pylover/fridgecon/schematic/fridgecon/fridgecon.kicad_sch

## KiCad design schematic/fridgecon/fridgecon.kicad_sch (2025-06-11, an earlier design)

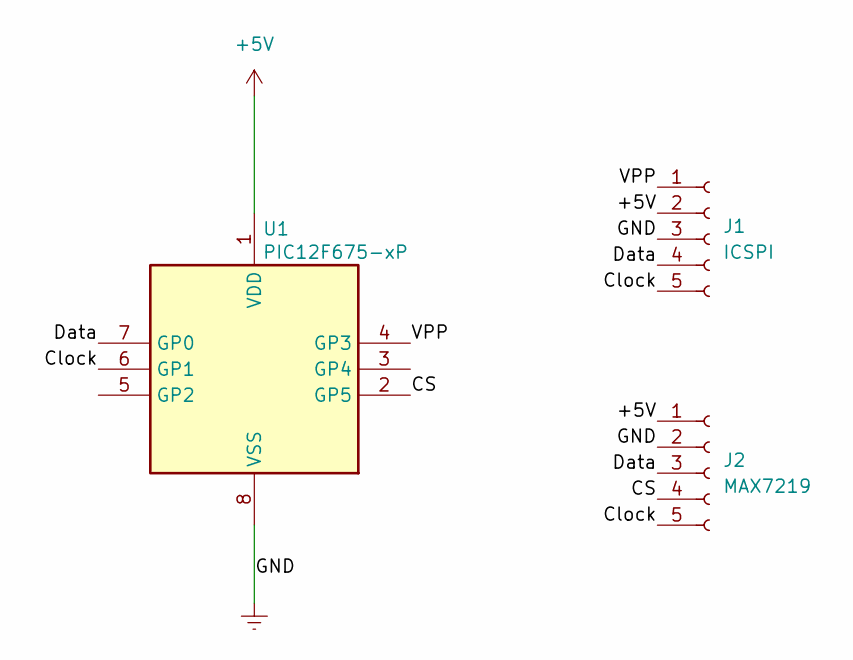
[picture p2: schematic fridgecon.kicad_sch]

Parts:
J1: ICSPI
J2: MAX7219
U1: PIC12F675-xP; DIP-8_W7.62mm

Connections:
+5V: J1.2, J2.1, U1.1 (VDD)
CS: J2.4, U1.2 (GP5)
Clock: J1.5, J2.5, U1.6 (GP1)
Data: J1.4, J2.3, U1.7 (GP0)
VPP: J1.1, U1.4 (GP3)
~: J1.3, J2.2, U1.8 (VSS)
